Void-Overflow/Face-Tracking-Camera/Demo Images and Video/IMG_9482.jpg

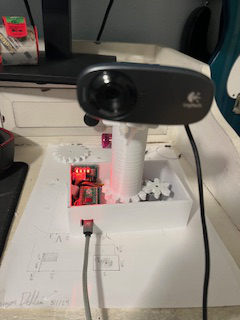
Demo Images and Video/IMG_9482.jpg
